3DES/WatchdogBoard/src/watchdog.cpp

#include <stdint.h>
#include "debug.hpp"
#include "watchdog.hpp"
#include "timer.hpp"
#include "errorAndDiagnosis.hpp"
#include "ioHandler.hpp"


// watchdog (re-)trigger time
#define WATCHDOG_VALUE_CLEAR 0
enum
{
    eWATCHDOG_VALUE_TRIGGER = 60000 / eTICK_TIME,   // eWATCHDOG_VALUE should be ~ 60 seconds, eTICK_TIME value is given in ms units
    eWATCHDOG_VALUE_CLEAR   = WATCHDOG_VALUE_CLEAR, // value to be set in error case (also Pi can set this value, e.g. in case it panics)
};


// reset lock release time after error, this time has to be long enough to ensure that the external battery switch off circuit has definitely switched OFF!
enum
{
    eLOCK_RESET   = 30000 / eTICK_TIME,   // when watchdog switches to error state the reset lock should be hold for several seconds (10000 = 10000ms)!
    eUNLOCK_RESET = 0,                    // reset can be unlocked again
};


// tick values until watchdog test is accepted as successful
enum {
    eSTATE_TICKS_COUNTER_END  = 0,
    eSTATE_TICKS_COUNTER_INIT = 3,  // number of ticks the expected read back state has to be seen without interruption
};


// timeout time during self test if expected test condition hasn't been detected
enum {
    eWATCHDOG_TEST_TIMEOUT_OVER = 0,
    eWATCHDOG_TEST_TIMEOUT_TIME = 10U * 1000,   // time until readback has to become 1 during initial test / become 0 during repeated test
};


// maximum time between self test requests
enum
{
    eWATCHDOG_TEST_REPEAT_TIME = 100UL * 60 * 60 * 1000,        // every 100h the output will be switched off what will be checked by monitoring the readback input
};


enum
{
    eWATCHDOG_TESTSTATE_INITIAL,                // initial test is running, the initial test is different from the repeated one, it only checks that readback is 0
    eWATCHDOG_TESTSTATE_REPEATED_EXPECT_ON,     // repeated test is running, the repeated test checks if readback is 1, then switches of the output and waits until the readback becomes 0
    eWATCHDOG_TESTSTATE_REPEATED_EXPECT_OFF,    // repeated test is running, the repeated test checks if readback is 1, then switches of the output and waits until the readback becomes 0

    eWATCHDOG_TESTSTATE_PASSED,                 // watchdog self test passed (wait until eWATCHDOG_TEST_REPEAT_TIME is over)
    eWATCHDOG_TESTSTATE_FAILED,                 // repeated test failed (it's a final state and will never be left again!)
};


static uint16_t watchdogCounter           = eWATCHDOG_VALUE_CLEAR;          // watchdog counter, during startup it's ok if the value is 0 but whenever it has been started it's not allowed to reach 0 again!
static uint8_t  watchDogState             = eWATCHDOG_STATE_INIT;           // curent watchdog state to decide if action is accepted or ignored
static uint16_t resetLockCounter          = eUNLOCK_RESET;                  // initially the reset port is not locked, when the watchdog is triggered reset port should be locked, when watchdog is cleared again the reset port should stay locked for a while


static bool selfTestConfirmation = false;                       // only if self test sets this to TRUE a selfTestApproval() will result in TRUE and the watchdog output is allowed to be switched ON

static uint16_t watchDogTestState = eWATCHDOG_TESTSTATE_INITIAL;    // initial state after start up
static bool watchDogTestRequested = false;                          // boolean to be set to true if request command has been received


enum
{
    eSELF_TEST_POLLING = 0,
    eSELF_TEST_TIMEOUT = 1,
    eSELF_TEST_OK      = 2,
};


enum
{
    eWATCHDOG_STATE_EXPECT_FALSE = false,
    eWATCHDOG_STATE_EXPECT_TRUE  = true,
};


/**
 * @brief Checks if readback port has expected state
 *
 * @param expectedReadbackState     state the readback port should have
 * @param readbackValue             state the readback port currently has
 * @return eSELF_TEST_POLLING       readback port not as expected but some polling time left
 * @return eSELF_TEST_OK            readback has expected state, polling finished
 * @return eSELF_TEST_TIMEOUT       timeout since readback didn't assume the expected state within time
 */
static uint16_t readBackPortPolling(bool expectedReadbackState, uint8_t readbackValue)
{
    static uint8_t stateCounter = eSTATE_TICKS_COUNTER_END;
    static uint16_t waitingTimeout = eWATCHDOG_TEST_TIMEOUT_OVER;

    uint16_t result = eSELF_TEST_POLLING;

    // if stateCounter is eSTATE_TICKS_COUNTER_END we entered a new test and have to set some initial values
    if (stateCounter == eSTATE_TICKS_COUNTER_END)
    {
        stateCounter = eSTATE_TICKS_COUNTER_INIT;
        waitingTimeout = eWATCHDOG_TEST_TIMEOUT_TIME;
    }

    // check if expectedReadbackState and readbackValue are identical (both OFF or both ON)
    if ((!readbackValue && !expectedReadbackState) || (readbackValue && expectedReadbackState))
    {
        stateCounter--;

        // at the end of the test stateCounter has to be 0
        if (stateCounter == eSTATE_TICKS_COUNTER_END)
        {
            // readback as expected
            result = eSELF_TEST_OK;
        }
    }
    else
    {
        // still polling...
        waitingTimeout--;

        // set state counter back to init value for the case there were some but not enough matching states in a single row
        stateCounter = eSTATE_TICKS_COUNTER_INIT;

        // give readback some more time to switch to expected state
        if (waitingTimeout == eWATCHDOG_TEST_TIMEOUT_OVER)
        {
            // at the end of the test stateCounter has to be 0 even if the test failed
            stateCounter = eSTATE_TICKS_COUNTER_END;

            // timeout happened
            result = eSELF_TEST_TIMEOUT;
        }
    }

    return result;
}


/**
 * @brief To switch wachdog into error state
 *
 */
static void switchWatchdogIntoErrorState(void)
{
    // stop watch dog even it's already been stopped
    noInterrupts();
    watchDogState = eWATCHDOG_STATE_ERROR;
    watchdogCounter = eWATCHDOG_VALUE_CLEAR;
    interrupts();
    //debug_pin2(LOW);  // #1

    // in ERROR case lock the reset pin for a while, so external timing relay can be switched OFF and even after a reset the battery cannot be started again without pressing a button manually!
    if (resetLockCounter != eUNLOCK_RESET)
    {
        //debug_pin1(LOW);  // #1
        resetLockCounter--;
        //debug_pin1(HIGH); // #1
    }
}


/**
 * @brief Requests self test
 *
 * @return true     in case watchdog is already running a test can be requested
 * @return false    in case watchdog is not running or a test is already in progress
 */
bool watchdog_requestSelfTest(void)
{
    bool requestPossible = false;
    if (watchDogTestState == eWATCHDOG_TESTSTATE_PASSED)
    {
        watchDogTestRequested = true;
        requestPossible = true;
    }

    return requestPossible;
}


/**
 * @brief Watchdog self test method has to be called always before watchdog state can be read otherwise watchdog state will always result to FALSE
 *
 * @param readbackValue     current value of readback input
 *
 * @return true     in case test was OK or test state needs watchdog to be switched ON
 * @return false    in case test failed or test state needs watchdog to be switched OFF
 */
void watchdog_selfTestHandler(uint8_t readbackValue)
{
    static uint32_t watchDogTestRemainingTime = 0UL;    // remaining time until next test will be executed (initially immediately when watchdog will be switched on, repeated test after eWATCHDOG_TEST_REPEAT_TIME ms)

    selfTestConfirmation = false;           // ensure watchdog cannot be switched ON except the following code decides that self test state is OK

    // execute watchdog test only if watchdog is not OFF (when watchdog is startet for the first time after startup it's frozen to zero until initial test has been finished)
    if (watchdog_readWatchdog())
    {
        switch (watchDogTestState)
        {
            // initially ensure watchdog is switched OFF (what means it can be switched off!)
            case eWATCHDOG_TESTSTATE_INITIAL:
                // wait for read back becomes OFF
                switch (readBackPortPolling(eWATCHDOG_STATE_EXPECT_FALSE, readbackValue))
                {
                    case eSELF_TEST_TIMEOUT:
                        // timeout during initial self test
                        errorAndDiagnosis_setError(eERROR_INITIAL_SELF_TEST_ERROR);
                        watchDogTestState = eWATCHDOG_TESTSTATE_FAILED;
                        break;

                    case eSELF_TEST_OK:
                        // initial self test passed
                        errorAndDiagnosis_setExecutedTest(eEXECUTED_TEST_SELF_TEST);
                        selfTestConfirmation = true;            // self test confirms that watchdog output can be switched ON (test was successful)
                        watchDogTestRemainingTime = eWATCHDOG_TEST_REPEAT_TIME;
                        watchDogTestState = eWATCHDOG_TESTSTATE_PASSED;
                        break;

                    // ignore the rest
                    default:
                        break;
                }
                break;

            case eWATCHDOG_TESTSTATE_REPEATED_EXPECT_ON:
                selfTestConfirmation = true;            // self test confirms that watchdog output can be switched ON (what is the expected state here)
                // wait for read back becomes ON
                switch (readBackPortPolling(eWATCHDOG_STATE_EXPECT_TRUE, readbackValue))
                {
                    case eSELF_TEST_TIMEOUT:
                        // timeout during repeated self test, watchdog is not OK, watchdog port is OFF
                        errorAndDiagnosis_setError(eERROR_REPEATED_SELF_TEST_ON_ERROR);
                        watchDogTestState = eWATCHDOG_TESTSTATE_FAILED;
                        break;

                    case eSELF_TEST_OK:
                        // first stage of repeated self test passed, watchdog is not in error state and watchdog port is ON!
                        watchDogTestState = eWATCHDOG_TESTSTATE_REPEATED_EXPECT_OFF;    // switch to next test state
                        break;

                    // ignore the rest
                    default:
                        break;
                }
                break;

            case eWATCHDOG_TESTSTATE_REPEATED_EXPECT_OFF:
            {
                switch (ioHandler_watchdogStopAndRetrigger())
                {
                    case eSTOP_AND_RETRIGGER_PASSED:
                        // second stage of repeated self test passed, watchdog output could be switched OFF
                        errorAndDiagnosis_setExecutedTest(eEXECUTED_TEST_SELF_TEST);
                        selfTestConfirmation = true;                                // self test confirms that watchdog output can be switched ON (test was successful)
                        watchDogTestRemainingTime = eWATCHDOG_TEST_REPEAT_TIME;     // reset time for next self test (100 hours)
                        watchDogTestState = eWATCHDOG_TESTSTATE_PASSED;             // finish test
                        break;

                    case eSTOP_AND_RETRIGGER_STOP_FAILED:
                        // timeout during repeated self test, watchdog output couldn't be switched OFF
                        watchDogTestState = eWATCHDOG_TESTSTATE_FAILED;
                        errorAndDiagnosis_setError(eERROR_REPEATED_SELF_TEST_OFF_ERROR);
                        break;

                    case eSTOP_AND_RETRIGGER_RETRIGGER_FAILED:
                        // timeout during repeated self test, watchdog output couldn't be switched ON again
                        watchDogTestState = eWATCHDOG_TESTSTATE_FAILED;
                        errorAndDiagnosis_setError(eERROR_REPEATED_SELF_TEST_RETRIGGER_ERROR);
                        break;
                }
                break;
            }

            // last self test passed so wait for next one
            case eWATCHDOG_TESTSTATE_PASSED:
                selfTestConfirmation = true;            // self test confirms that watchdog output can be switched ON (last test was successful and there is still some time until it has to be executed for the next time)
                if (watchDogTestRequested)
                {
                    // new test requested
                    watchDogTestRequested = false;
                    watchDogTestState = eWATCHDOG_TESTSTATE_REPEATED_EXPECT_ON;     // switch to next test state
                }
                else if (watchDogTestRemainingTime)
                {
                    // still some time left since self test has been executed the last time
                    watchDogTestRemainingTime--;
                }
                else
                {
                    // time since last self test is over an no further one has been requested
                    errorAndDiagnosis_setError(eERROR_REPEATED_SELF_TEST_REQUEST_MISSED);
                    watchDogTestState = eWATCHDOG_TESTSTATE_FAILED;
                }
                break;

            // watchdog cannot be switched ON again (since selfTestConfirmation will never become TRUE if we are here), a reset is necessary!
            case eWATCHDOG_TESTSTATE_FAILED:
                switchWatchdogIntoErrorState();
                break;
        }
    }
}


/**
 * @brief Check if self test approval is available but approval will be cleared after checked once and has to be requested again by calling watchdog_selfTestHandler()
 *
 * @return true     self test approval is available
 * @return false    self test approval is NOT available
 */
static inline bool selfTestApproval(void)
{
    bool selfTestConfirmationTemp = selfTestConfirmation;
    selfTestConfirmation = false;

    return selfTestConfirmationTemp;
}


/**
 * @brief Set watchdog state
 *
 * @param value != 0    triggers watchdog if watchdog is not yet in ERROR state
 * @param value == 0    stops watchdog and switches watchdog into ERROR state
 */
void watchdog_setWatchdog(uint16_t value)
{
    /*
     * Watchdog states and state changes:
     *
     *            |   INIT    |     OK     |   ERROR
     * -----------|-----------|------------|-----------
     * value = 0  | value = 0 | value = 0  | ignore
     * -----------|-----------|------------|-----------
     * value != 0 | value = n | value = n  | ignore
     */
    if (watchDogState != eWATCHDOG_STATE_ERROR)
    {
        if (value)
        {
            // set watch dog values
            noInterrupts();
            watchdogCounter  = eWATCHDOG_VALUE_TRIGGER;
            resetLockCounter = eLOCK_RESET;             // lock reset port as soon as watchdog has been started
            watchDogState = eWATCHDOG_STATE_OK;
            interrupts();
            //debug_pin2(HIGH); // #1
        }
        else
        {
            // value == 0 is only OK during init phase but afterwards it must be an error detected by someone externally that switches the watchdog OFF now
            if (watchDogState != eWATCHDOG_STATE_INIT)
            {
                switchWatchdogIntoErrorState();         // clearing the watchdog is also a watchdog error and retriggering is not possible anymore

                // watchdog cleared via command
                errorAndDiagnosis_setError(eERROR_WATCHDOG_CLEARED);
            }
        }
    }
}


/**
 * @brief read current watch dog state
 *
 * @return true     watchdog is running
 * @return false    watchdog is not running, watchdog can be in ERROR or in INIT state
 */
bool watchdog_readWatchdog(void)
{
#if defined DEBUG && defined ALWAYS_RUNNING
    static bool onceTrue = false;
    if (watchdogCounter != eWATCHDOG_VALUE_CLEAR)
    {
        // if watchdog was true once, it will never become false again, so init phase is fully simulated but then all errors are ignored
        onceTrue = true;
    }
    return onceTrue;
#else
    return (watchdogCounter != eWATCHDOG_VALUE_CLEAR);
#endif
}


/**
 * @brief watchdog trigger, each call decrements the watchdog, has to be called every millisecond!
 */
bool watchdog_trigger(void)
{

#if WATCHDOG_VALUE_CLEAR != 0
#   error WATCHDOG_VALUE_CLEAR is expected to be defined as 0 otherwise the following algorithm will not work
#endif

    // decrement until eWATCHDOG_VALUE_CLEAR will be reached
    if (watchdog_readWatchdog())
    {
        noInterrupts();
        watchdogCounter--;       // this expects that watchdog == 0 and watchdog == WATCHDOG_VALUE_CLEAR means the same!
        interrupts();

        // watchdog counter became zero
        if (!watchdog_readWatchdog())
        {
            errorAndDiagnosis_setError(eERROR_WATCHDOG_NOT_TRIGGERED);
            switchWatchdogIntoErrorState();
        }
    }

    // since this method is called periodically do an overall check if watchdog is in ERROR state (defensive programming... yes we want this here!)
    if (!watchdog_readWatchdog() && (watchDogState != eWATCHDOG_STATE_INIT))
    {
        if (watchDogState == eWATCHDOG_STATE_OK)
        {
            errorAndDiagnosis_setError(eERROR_WATCHDOG_STOPPED_UNEXPECTEDLY);
        }
        switchWatchdogIntoErrorState();
    }

    // decide if watchdog port has to be switched ON or OFF (OFF is not always an error since even during self test it has to be switched OFF for a short period of time)
    return selfTestApproval() && watchdog_readWatchdog();
}


/**
 * @brief get current watchdog state
 *
 * @return 0 = watchdog output is OFF (not yet set or still OFF after reset)
 * @return 1 = watchdog output is ON (= ok)
 */
uint8_t watchdog_getState(void)
{
    return watchDogState;
}


/**
 * @brief To check if reset port has to be locked or not
 *
 * @return true     reset port has to be locked, no reset is allowed
 * @return false    reset port can be unlocked, reset is allowed
 */
bool watchdog_resetPortMustBeLocked(void)
{
    return (resetLockCounter != eUNLOCK_RESET);        // lock until resetLockCounter variable reaches eUNLOCK_RESET value
}
