3DES/WatchdogBoard/src/ioHandler.hpp

#if not defined IO_HANDLER_H
#define IO_HANDLER_H


#define SUPPORTED_OUTPUTS 7
#define SUPPORTED_INPUTS  4


enum
{
    D0  = 0,
    D1  = 1,
    D2  = 2,
    D3  = 3,
    D4  = 4,
    D5  = 5,
    D6  = 6,
    D7  = 7,
    D8  = 8,
    D9  = 9,
    D10 = 10,
    D11 = 11,
    D12 = 12,
    D13 = 13,
};


enum
{
    eSUPPORTED_OUTPUTS = SUPPORTED_OUTPUTS,     // watchdog is not an output, so there are only 7 of them!
    eSUPPORTED_INPUTS  = SUPPORTED_INPUTS,      // 4 inputs are available!
};


// return values of ioHandler_watchdogStopAndRetrigger()
enum
{
    eSTOP_AND_RETRIGGER_PASSED = 0,
    eSTOP_AND_RETRIGGER_STOP_FAILED = 1,
    eSTOP_AND_RETRIGGER_RETRIGGER_FAILED = 2,
};


void ioHandler_setup(void);

void ioHandler_setOutput(uint16_t index, uint8_t value);
bool ioHandler_getOutput(uint16_t index);
bool ioHandler_getInput(uint16_t index);

uint8_t ioHandler_watchdogStopAndRetrigger(void);


void ioHandler_cyclicTask();


#endif
